creative-computational-architecture/plug-in-parasite/cinematic/concept_boards/00_MASTER_inhabit_clean.jpg

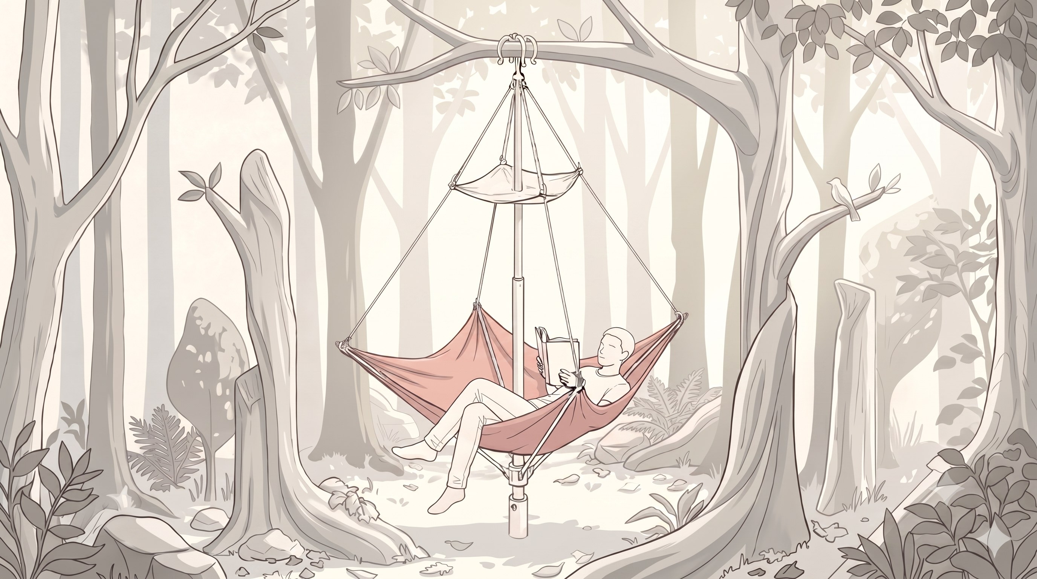
cinematic/concept_boards/00_MASTER_inhabit_clean.jpg
