creative-computational-architecture/plug-in-parasite/cinematic/concept_boards/02_EXTEND.jpg

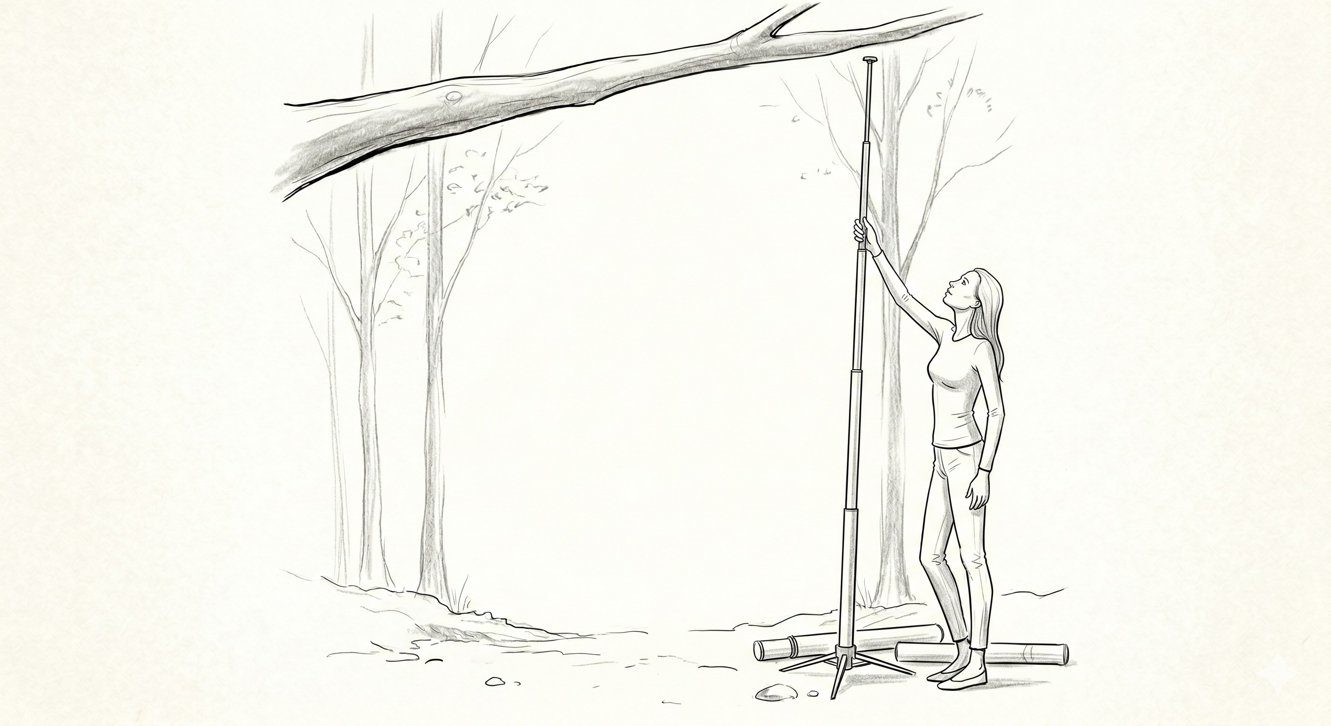
cinematic/concept_boards/02_EXTEND.jpg
