creative-computational-architecture/plug-in-parasite/cinematic/drawings/deployment_preview.png

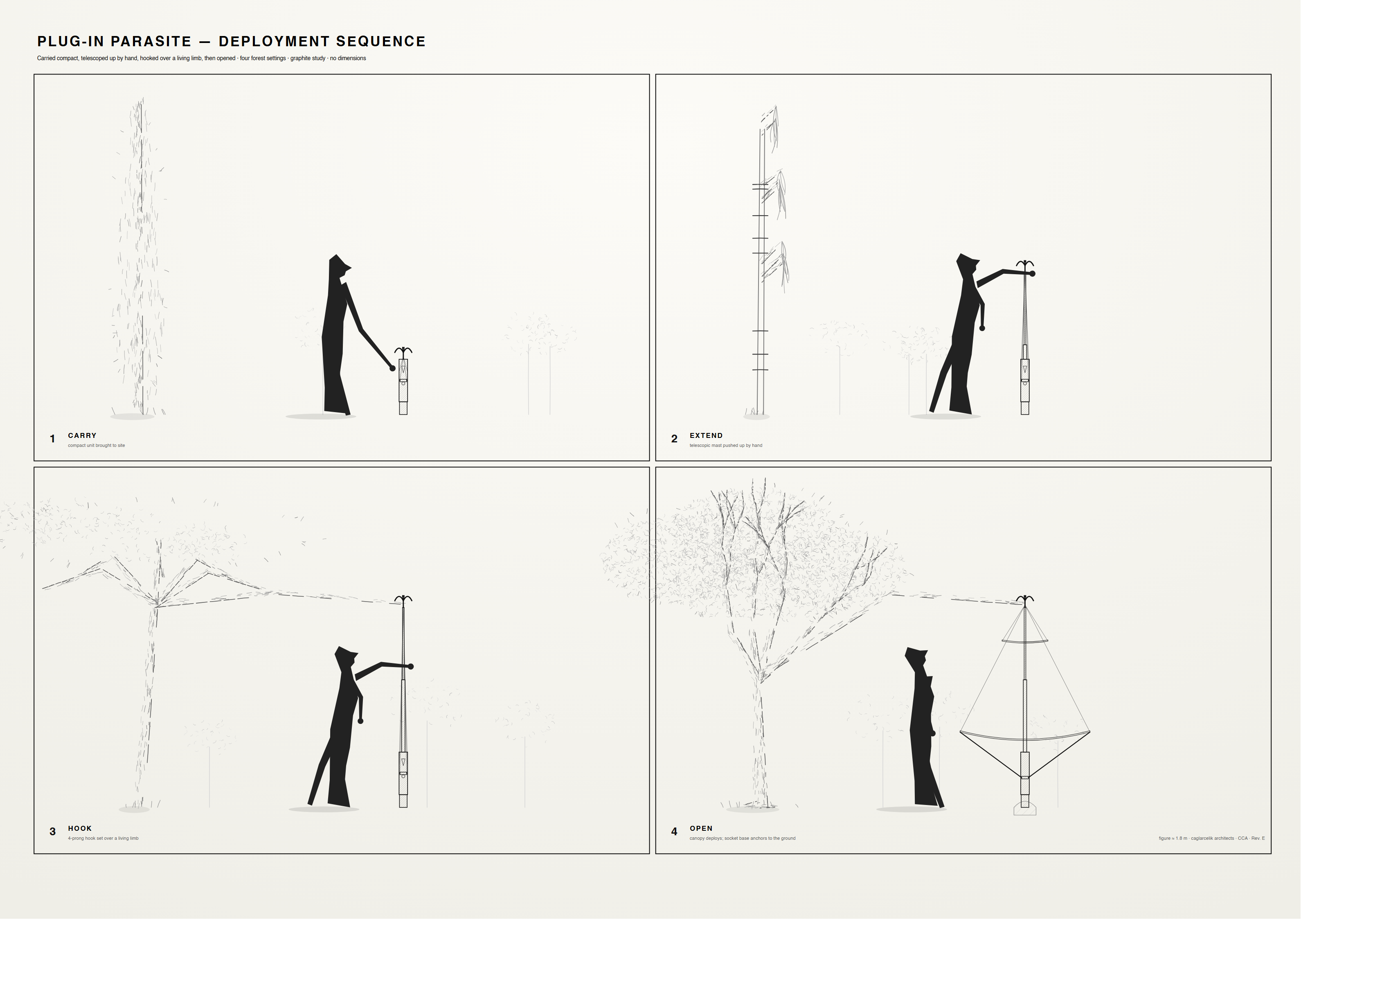
cinematic/drawings/deployment_preview.png
