creative-computational-architecture/plug-in-parasite/cinematic/drawings/PlugInParasite_branch_detail.png

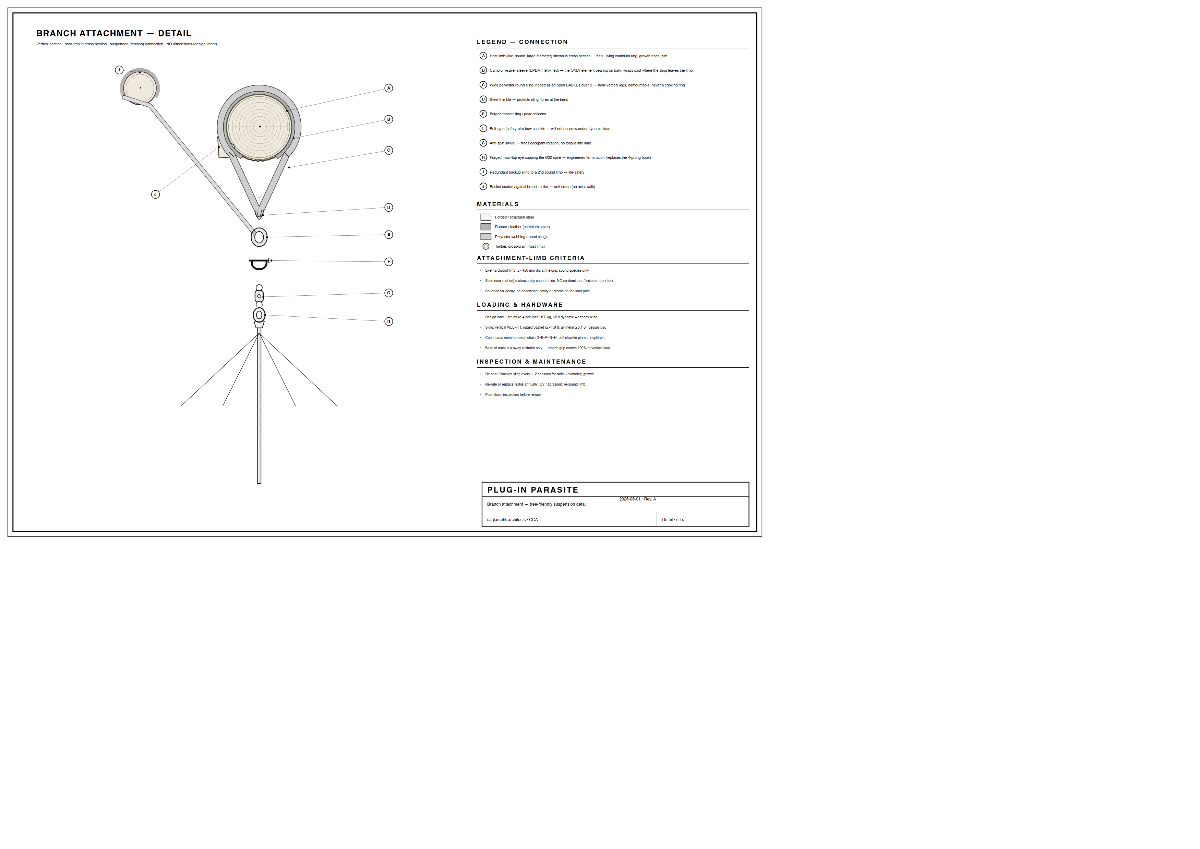
cinematic/drawings/PlugInParasite_branch_detail.png
