creative-computational-architecture/plug-in-parasite/cinematic/drawings/PlugInParasite_section_plate.png

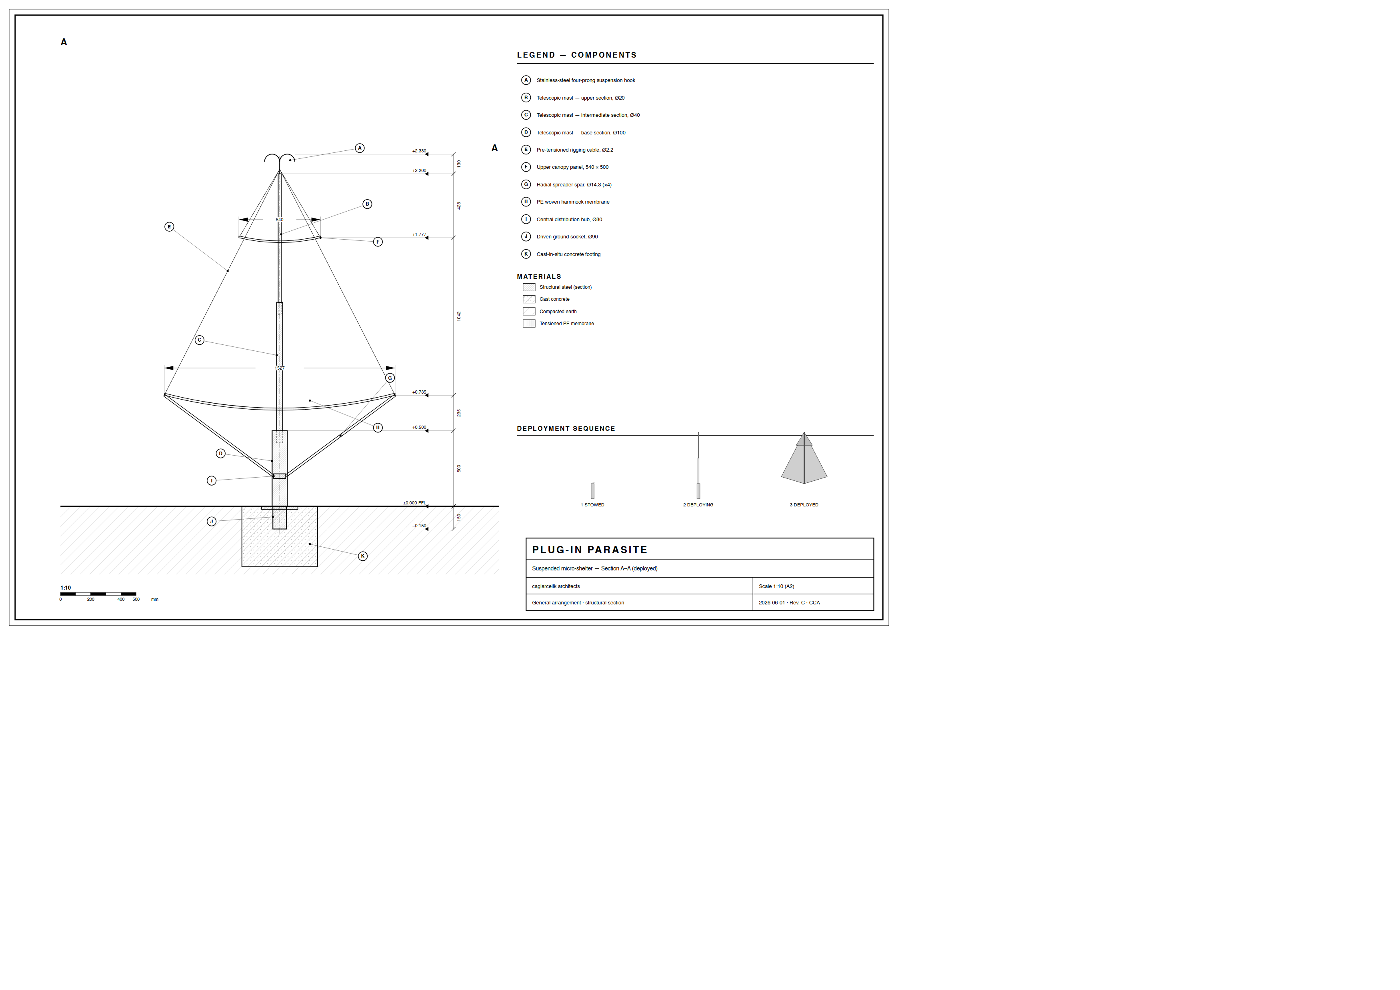
cinematic/drawings/PlugInParasite_section_plate.png
