creative-computational-architecture/plug-in-parasite/cinematic/geometry_ref/deployed_clay.png

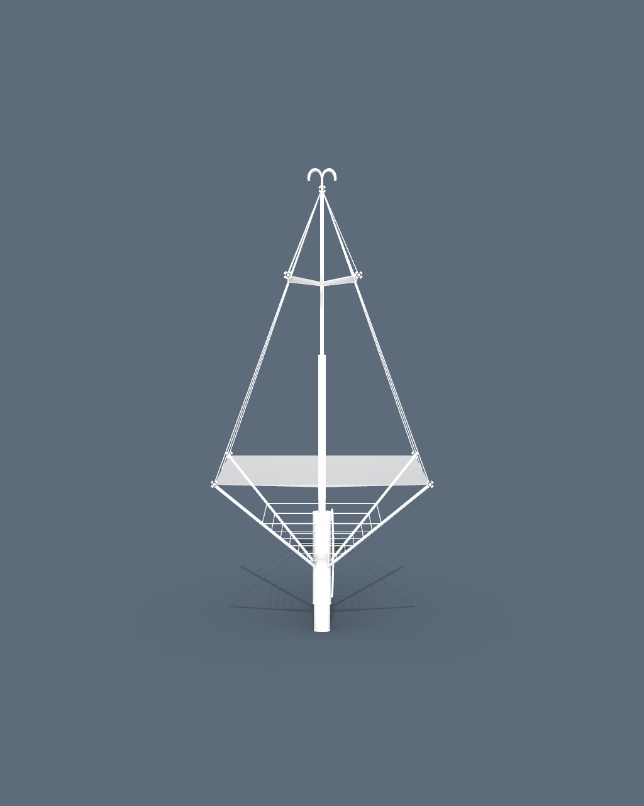
cinematic/geometry_ref/deployed_clay.png
