creative-computational-architecture/plug-in-parasite/cinematic/geometry_ref/deployed_edged.png

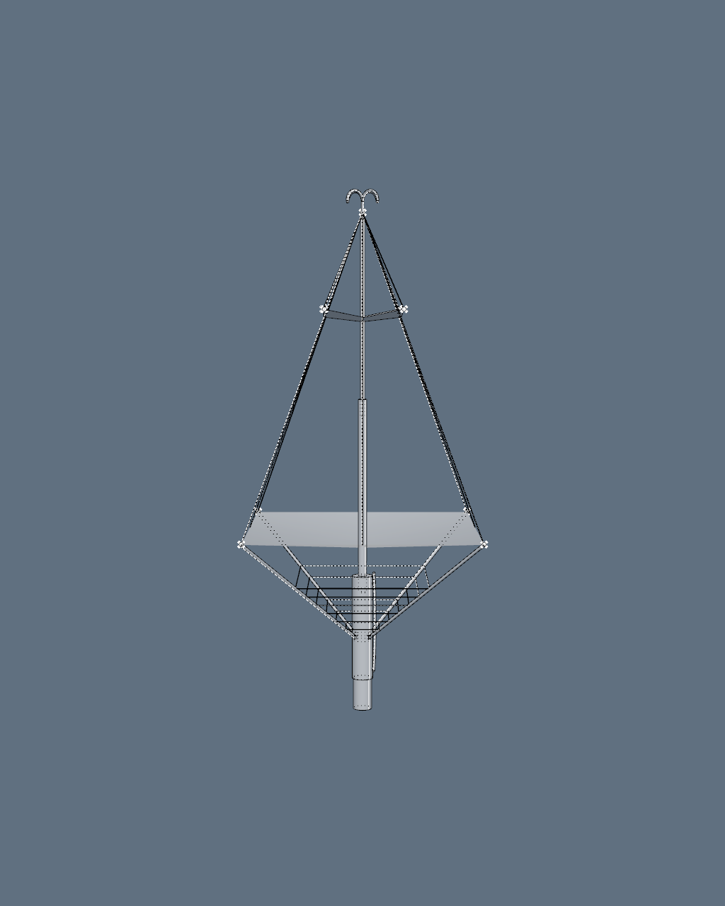
cinematic/geometry_ref/deployed_edged.png
