creative-computational-architecture/plug-in-parasite/cinematic/geometry_ref/extended_clay.png

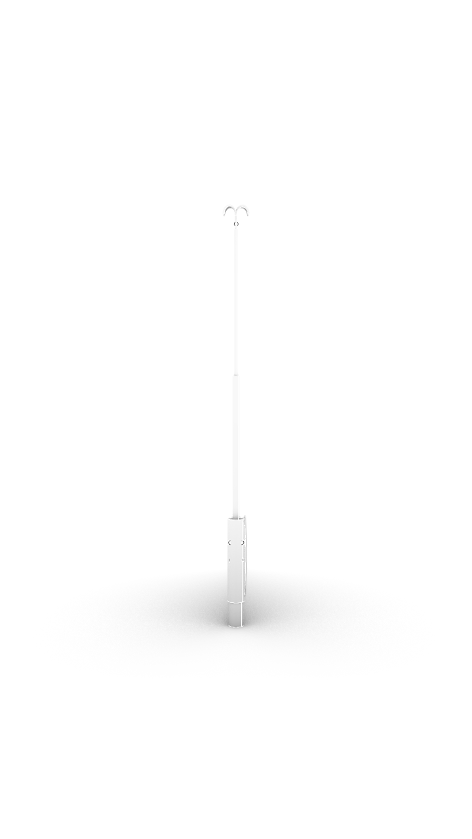
cinematic/geometry_ref/extended_clay.png
