creative-computational-architecture/plug-in-parasite/cinematic/geometry_ref/folded_clay.png

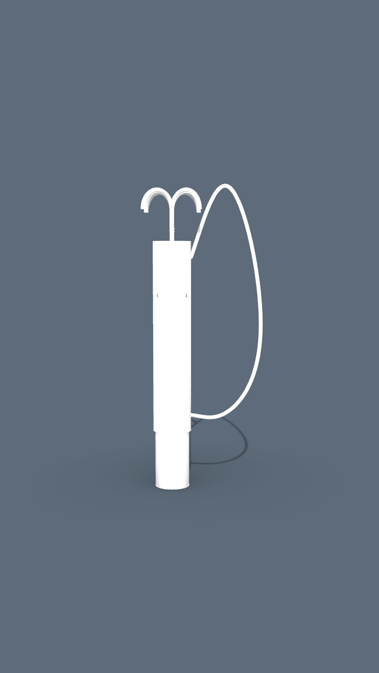
cinematic/geometry_ref/folded_clay.png
