creative-computational-architecture/plug-in-parasite/cinematic/geometry_ref/hook_closeup.png

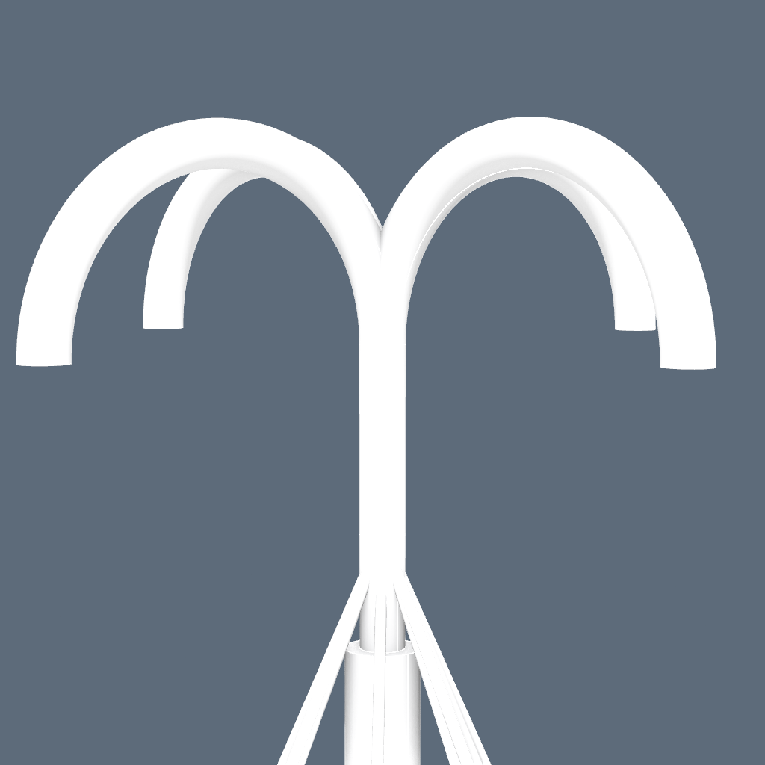
cinematic/geometry_ref/hook_closeup.png
