creative-computational-architecture/plug-in-parasite/images/deck/page-2.jpg

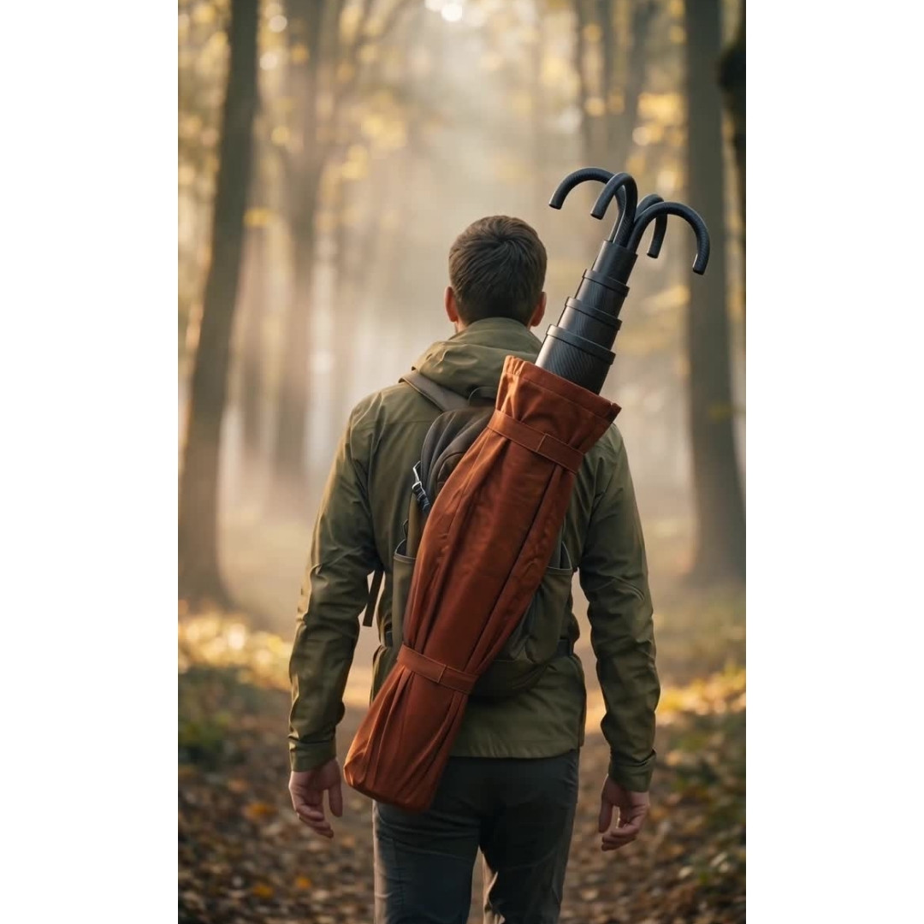
images/deck/page-2.jpg
