creative-computational-architecture/plug-in-parasite/images/deck/page-3.jpg

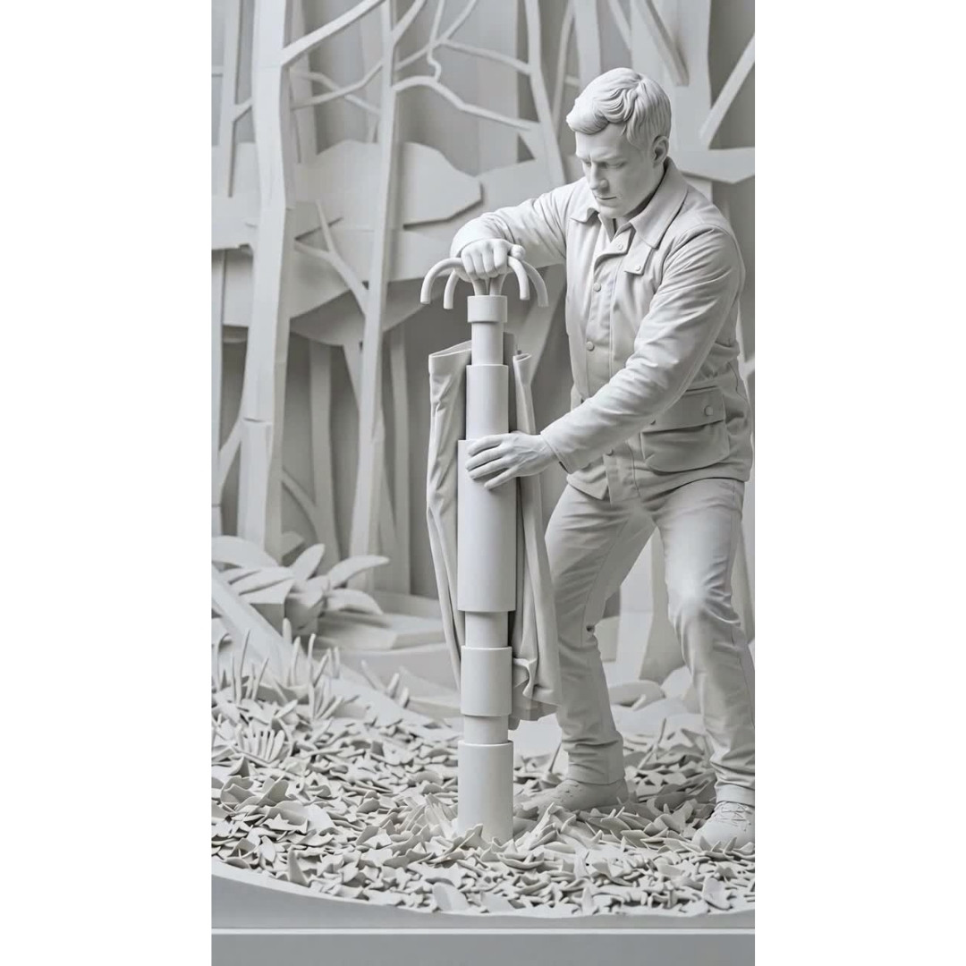
images/deck/page-3.jpg
