creative-computational-architecture/plug-in-parasite/images/deck/page-4.jpg

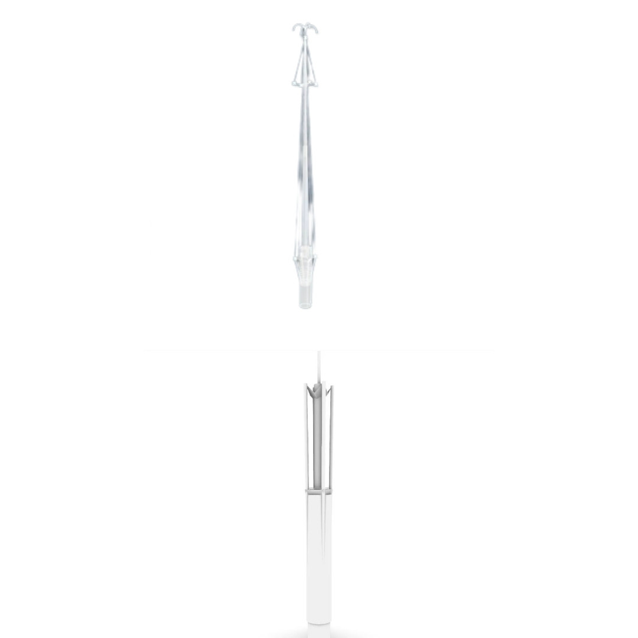
images/deck/page-4.jpg
