creative-computational-architecture/plug-in-parasite/images/deck/page-6.jpg

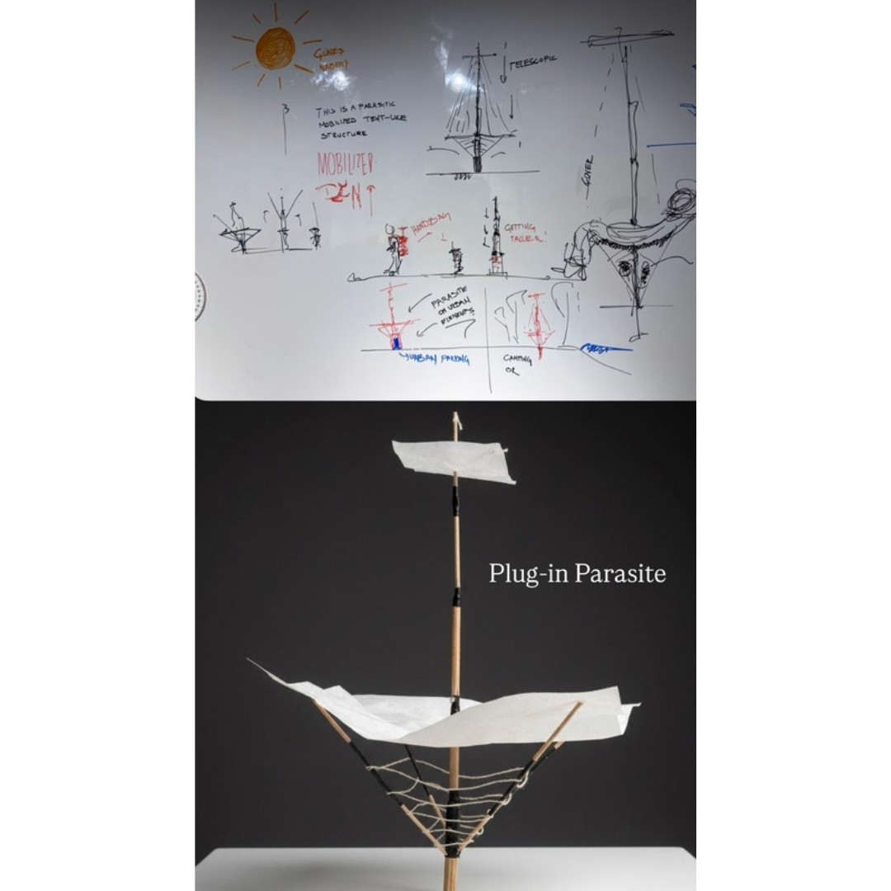
images/deck/page-6.jpg
